krebyy/ton-fit/images/ton-fit_v2_bot.png

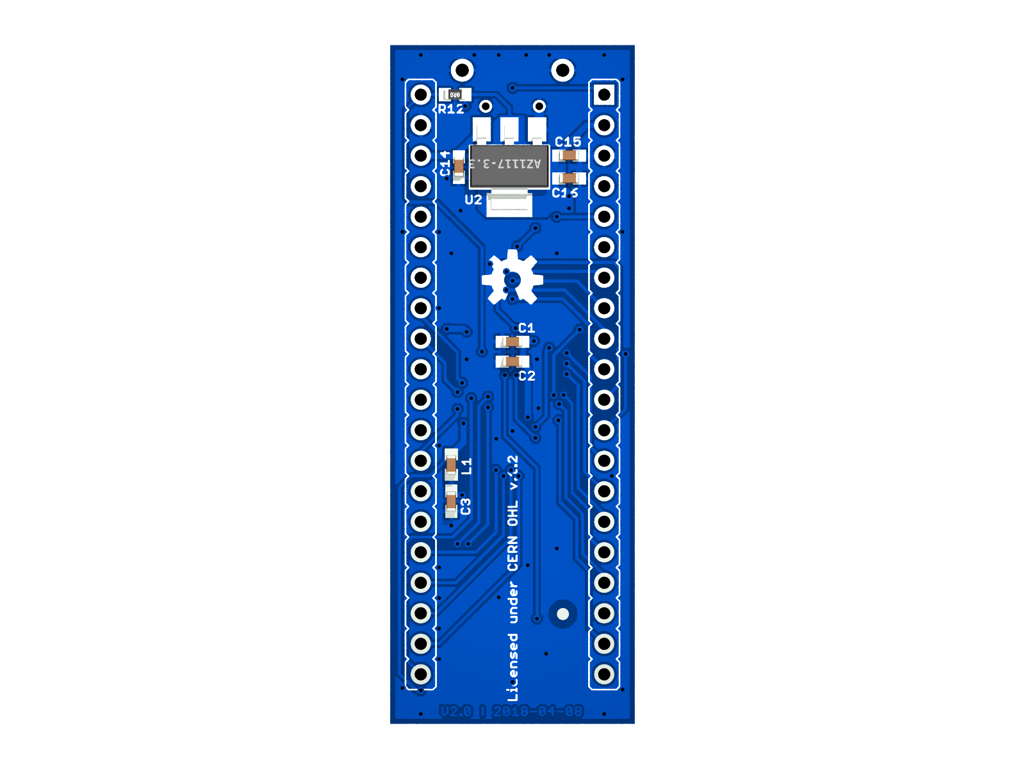
images/ton-fit_v2_bot.png
